Elecrow-RD/CrowPanel-2.4-ESP32-HMI-320x240/2.4_hmi_display.jpg

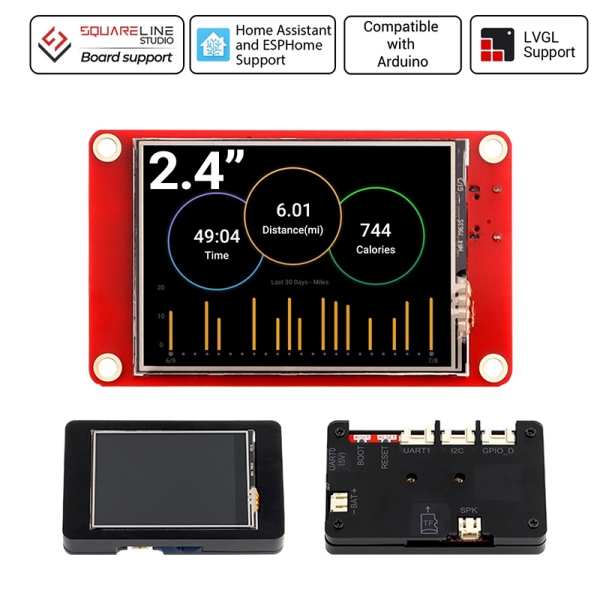
2.4_hmi_display.jpg
