Elecrow-RD/CrowPanel-2.4-ESP32-HMI-320x240/arduino1.jpg

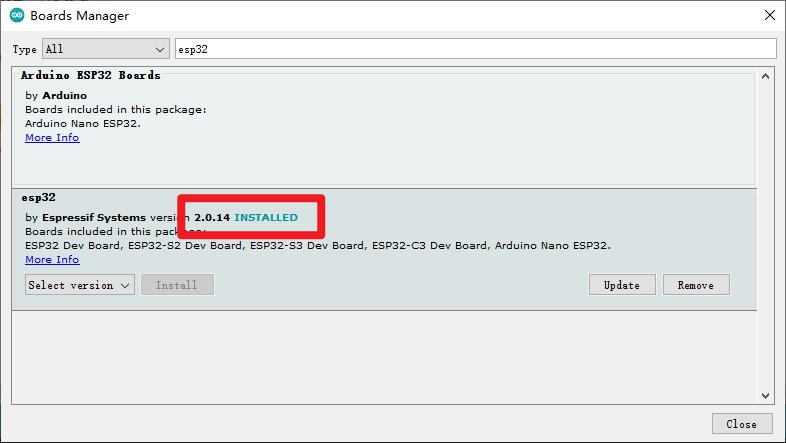
arduino1.jpg
