Elecrow-RD/CrowPanel-2.4-ESP32-HMI-320x240/arduino2.jpg

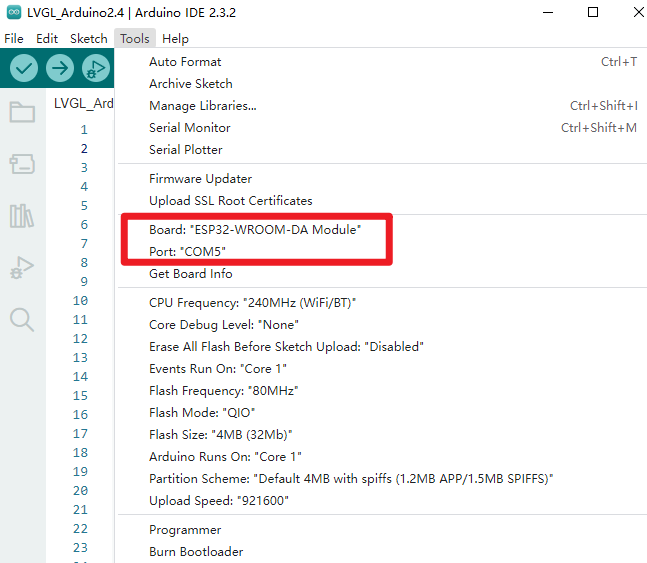
arduino2.jpg
