Elecrow-RD/CrowPanel-2.4-ESP32-HMI-320x240/example/V2.1/Arduino/Course/LVGL_Arduino2.4/LVGL-Assets-320x240/background.png

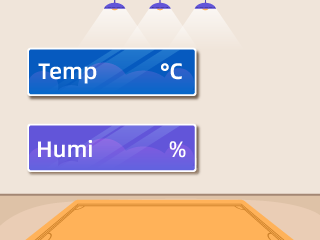
example/V2.1/Arduino/Course/LVGL_Arduino2.4/LVGL-Assets-320x240/background.png
