Elecrow-RD/CrowPanel-2.4-ESP32-HMI-320x240/factory_firmware/flash1.jpg

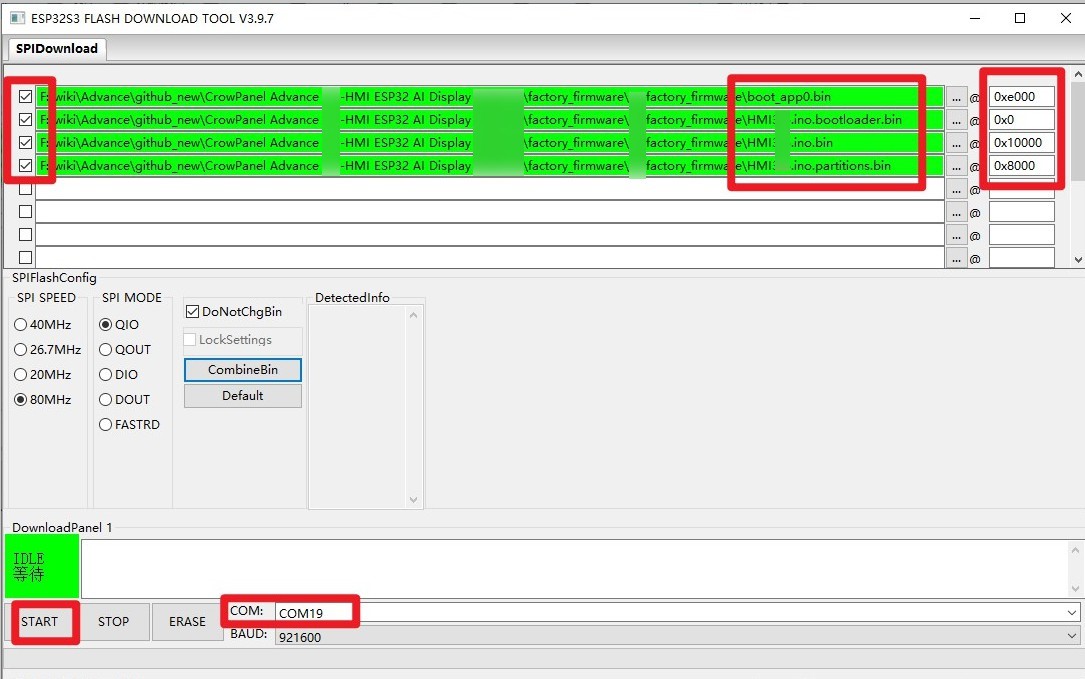
factory_firmware/flash1.jpg
