Elecrow-RD/CrowPanel-2.4-ESP32-HMI-320x240/example/V1.0_and_V2.0/Arduino/Arduino_Tutorial_24/2.4-Examples/SPEAK/A-2.4-SPEAK/A-2.4-SPEAK.ino

#include "MusicDefinitions.h"
#include "SoundData.h"
#include "XT_DAC_Audio.h"


//SPEAK
// Data for the melody. Note followed by optional change in playing length in 1/4 beats. See documentation for more details
int8_t PROGMEM TwinkleTwinkle[] = {
  NOTE_C5, NOTE_C5, NOTE_G5, NOTE_G5, NOTE_A5, NOTE_A5, NOTE_G5, BEAT_2,
  NOTE_F5, NOTE_F5, NOTE_E5, NOTE_E5, NOTE_D5, NOTE_D5, NOTE_C5, BEAT_2,
  NOTE_G5, NOTE_G5, NOTE_F5, NOTE_F5, NOTE_E5, NOTE_E5, NOTE_D5, BEAT_2,
  NOTE_G5, NOTE_G5, NOTE_F5, NOTE_F5, NOTE_E5, NOTE_E5, NOTE_D5, BEAT_2,
  NOTE_C5, NOTE_C5, NOTE_G5, NOTE_G5, NOTE_A5, NOTE_A5, NOTE_G5, BEAT_2,
  NOTE_F5, NOTE_F5, NOTE_E5, NOTE_E5, NOTE_D5, NOTE_D5, NOTE_C5, BEAT_4,
  NOTE_SILENCE, BEAT_5, SCORE_END
};
XT_DAC_Audio_Class DacAudio(26, 0);         // Create the main player class object. Use GPIO 25, one of the 2 DAC pins and timer 0
XT_Wav_Class ForceWithYou(Force);           // create WAV object and pass in the WAV data
XT_MusicScore_Class Music(TwinkleTwinkle, TEMPO_ALLEGRO, INSTRUMENT_PIANO); // The music score object, pass in the Music data
XT_Sequence_Class Sequence;                // The sequence object, you add your sounds above to this object (see setup below)

void setup() {
  // put your setup code here, to run once:
  Serial.begin( 9600 ); 
  Sequence.AddPlayItem(&ForceWithYou);      // Add the first sound item, this will play first
  Sequence.AddPlayItem(&Music);             // Add the music score, this will play after the first item
  DacAudio.Play(&Sequence);                 // Play the sequence, will play just the once and then stop
}

void loop() {
  // put your main code here, to run repeatedly:
  DacAudio.FillBuffer();//Play
  //  DacAudio.StopAllSounds(); //Stop Playing
}
